fussdeek-del/Broccoli-board/img assets/AI generated final look 2.jpg

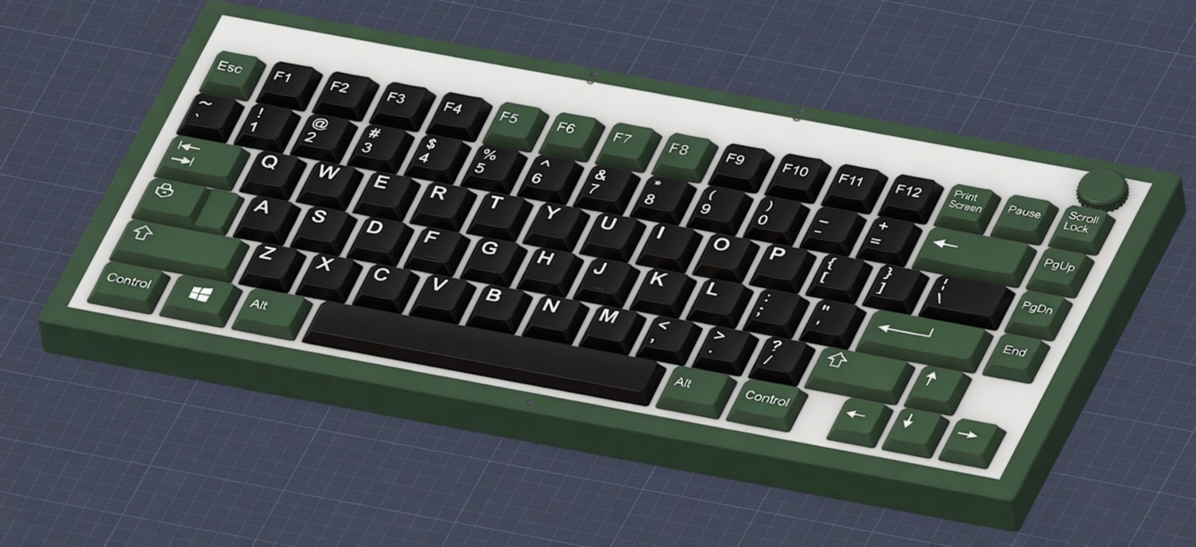
img assets/AI generated final look 2.jpg
