fussdeek-del/Broccoli-board/img assets/cover.png

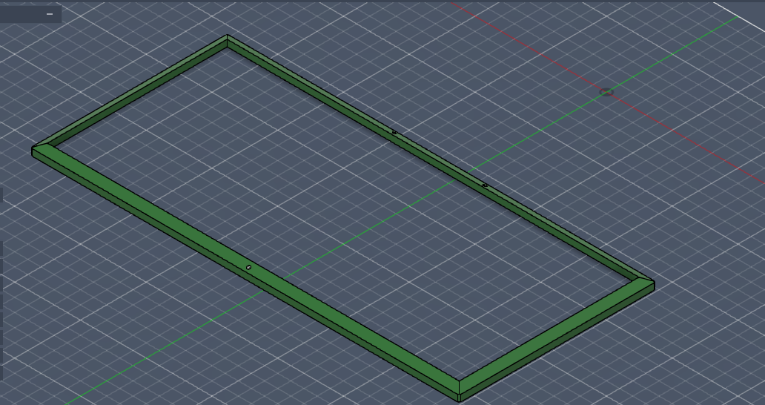
img assets/cover.png
