fussdeek-del/Broccoli-board/img assets/LEDs sch.png

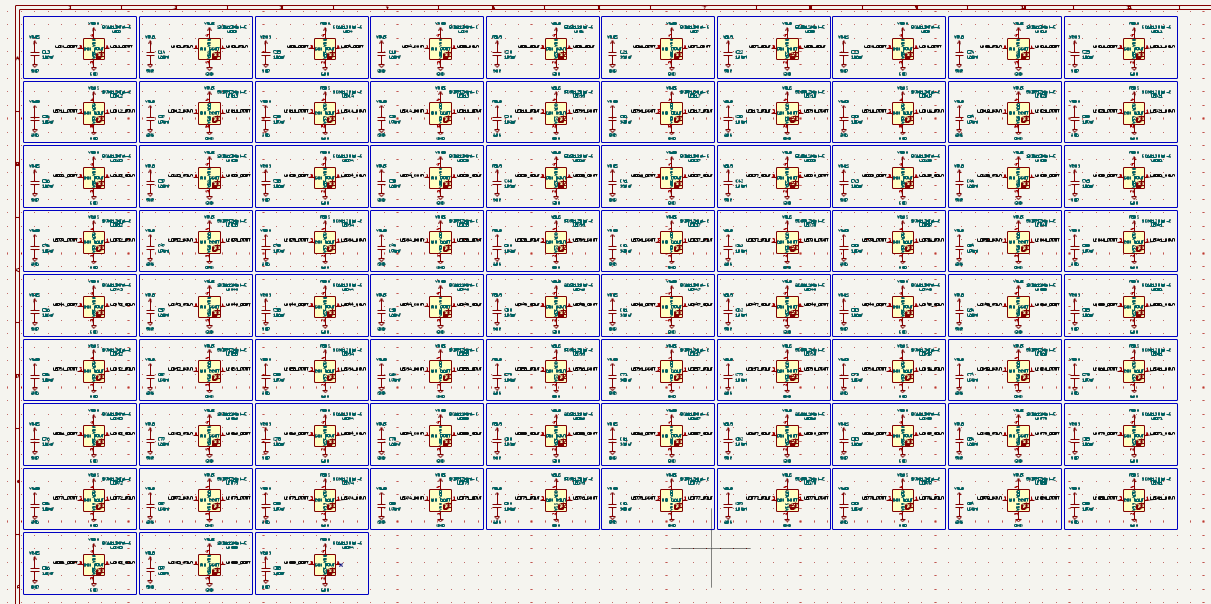
img assets/LEDs sch.png
