fussdeek-del/Broccoli-board/img assets/plate.png

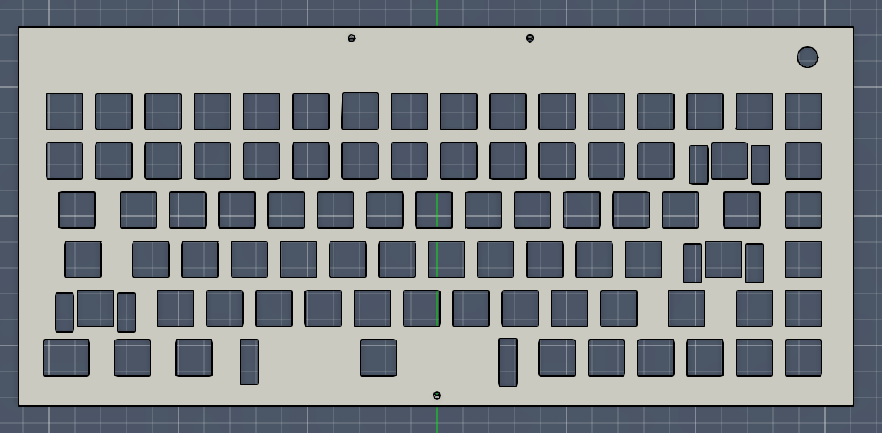
img assets/plate.png
