fussdeek-del/Broccoli-board/img assets/power system sch.png

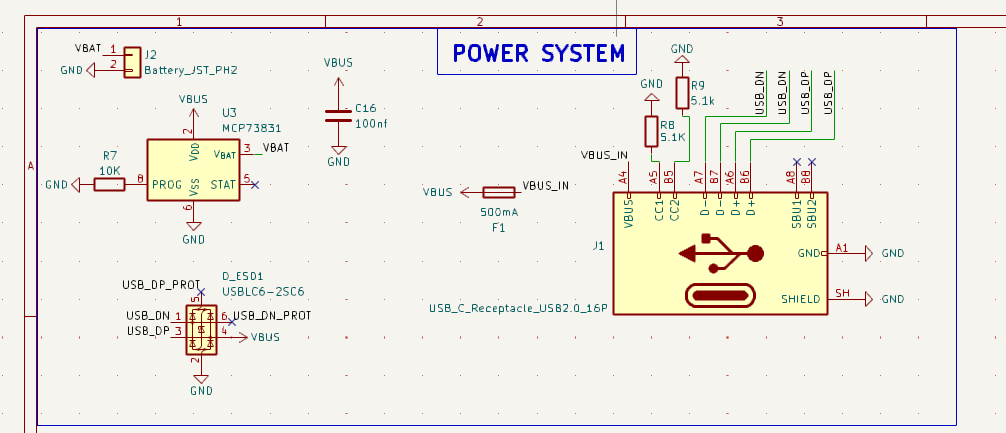
img assets/power system sch.png
