fussdeek-del/Broccoli-board/img assets/RGB lvl shifter sch.png

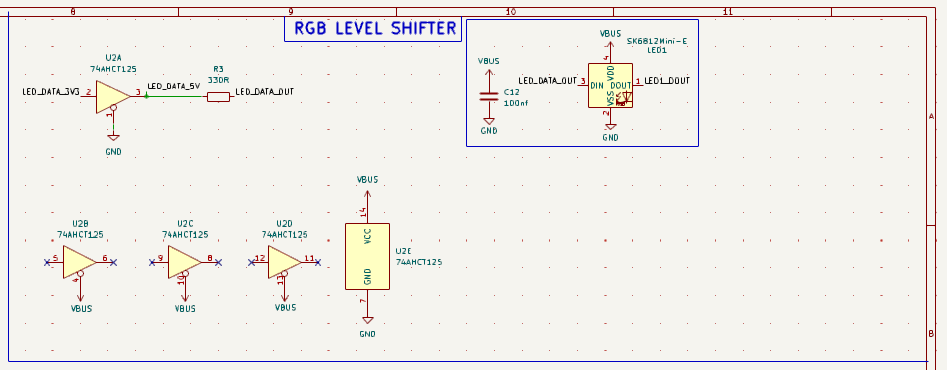
img assets/RGB lvl shifter sch.png
