fussdeek-del/Broccoli-board/img assets/Tray back.png

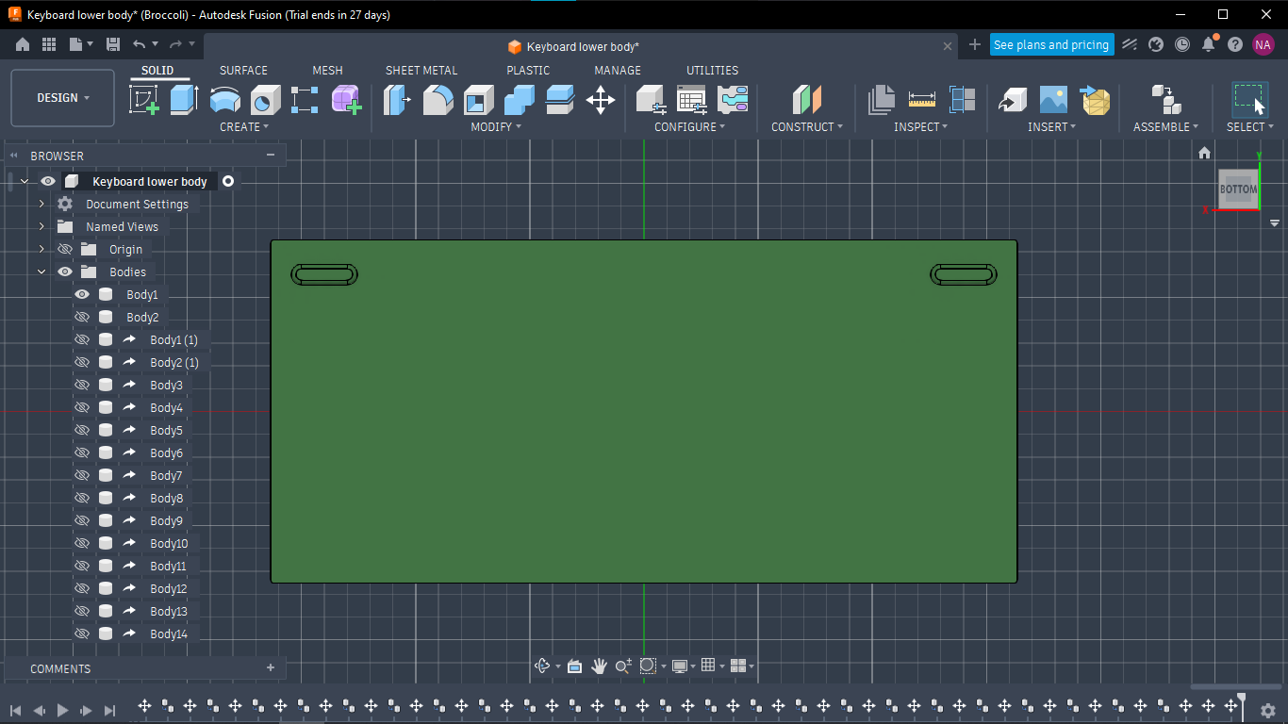
img assets/Tray back.png
